saiprashanth802/ESP32-BLE-Macropad/cad/stl/keycap/keycap_v3.stl

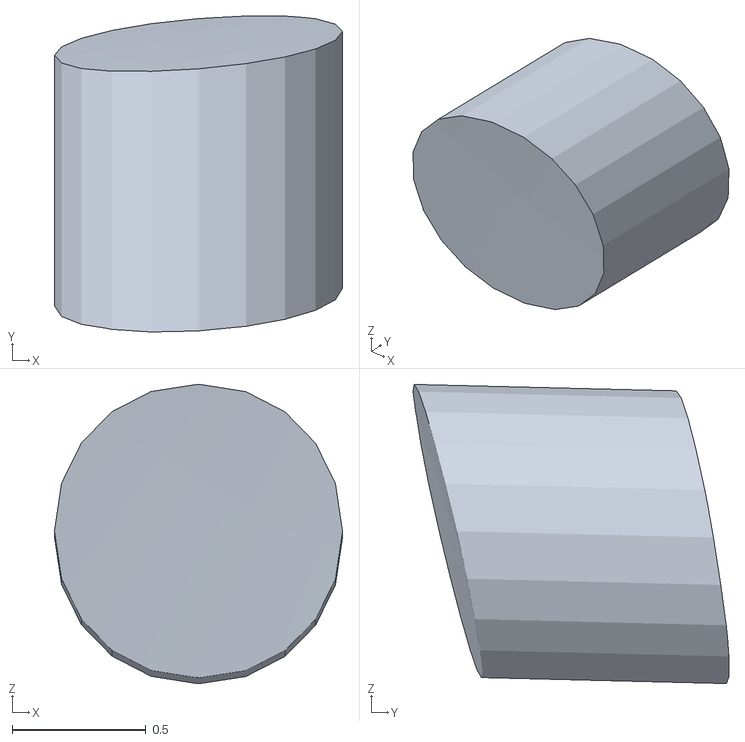
[picture p29: CAD file, 2026-04-09, an earlier design]
cad/stl/keycap/keycap_v3.stl
1.08 x 1.18 x 1.12
